sachiniyer/Electric-Trombone/v3/E-bone3/model/gear.stl

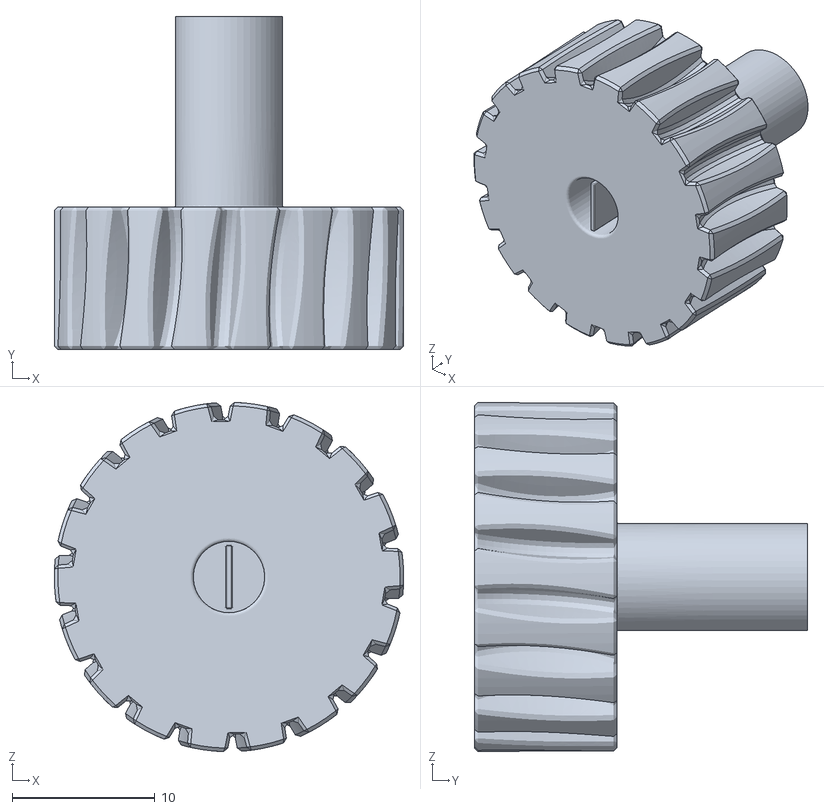
[picture p16: CAD file, 2021-02-16, an earlier design]
v3/E-bone3/model/gear.stl
24.5 x 23.3 x 24.5
