sachiniyer/Electric-Trombone/v2/E-bone2/Models/models/spring.stl

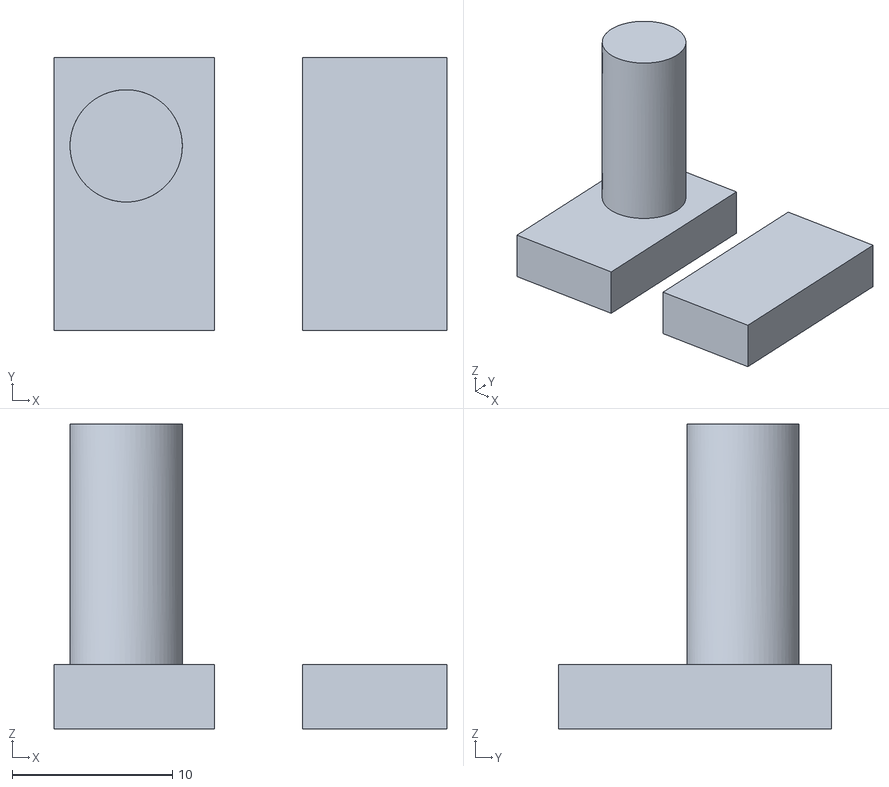
[picture p17: CAD file, 2021-02-16, an earlier design]
v2/E-bone2/Models/models/spring.stl
24.5 x 17.0 x 19.0
