sachiniyer/Electric-Trombone/v2/E-bone2/models/shaft.stl

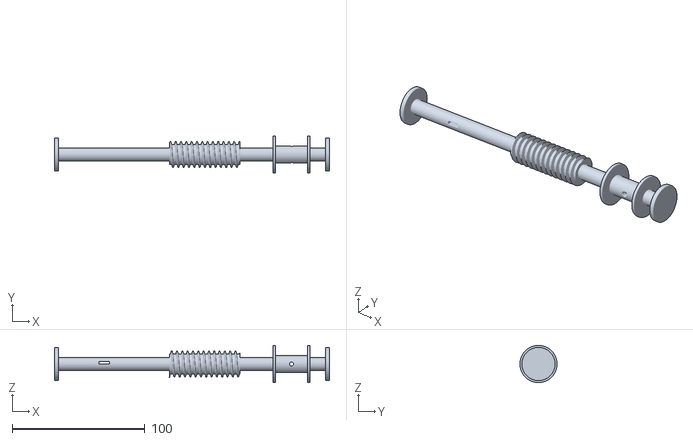
[picture p18: CAD file, 2021-02-16, an earlier design]
v2/E-bone2/models/shaft.stl
207.0 x 28.0 x 28.0
